braingeneers/incubatormicroscopesupplement/CAD/flatparts/midbot_countersink_xyz.dxf

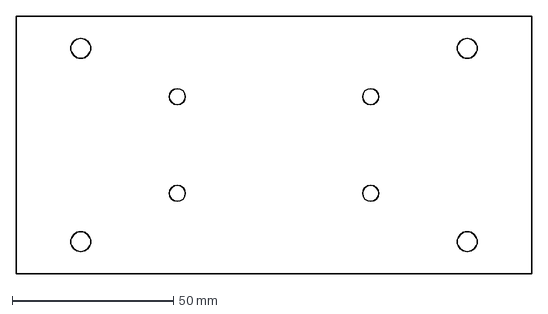
[picture p14: CAD file, 2026-02-16]
CAD/flatparts/midbot_countersink_xyz.dxf
160.0 x 80.0 mm
