braingeneers/incubatormicroscopesupplement/CAD/flatparts/endstophitter_short_xyz.dxf

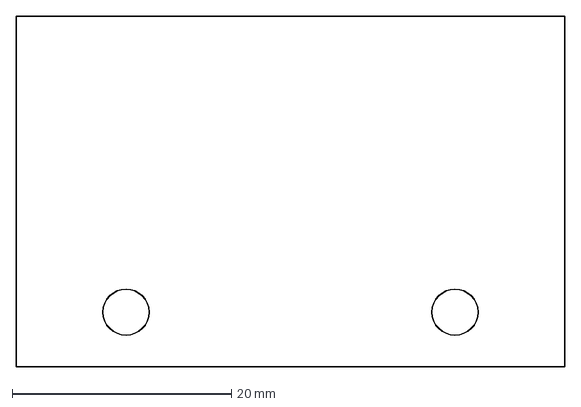
[picture p15: CAD file, 2026-02-16]
CAD/flatparts/endstophitter_short_xyz.dxf
50.0 x 32.0 mm
