braingeneers/incubatormicroscopesupplement/CAD/flatparts/endstopholder_Z.dxf

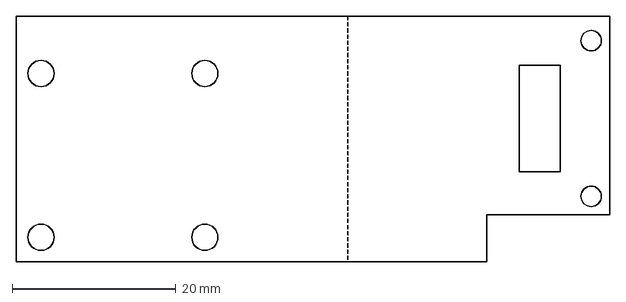
[picture p16: CAD file, 2025-06-12]
CAD/flatparts/endstopholder_Z.dxf
72.4 x 30.0 mm
